guberti/CockcroftWalton/photos/IMG_20190924_183516.jpg

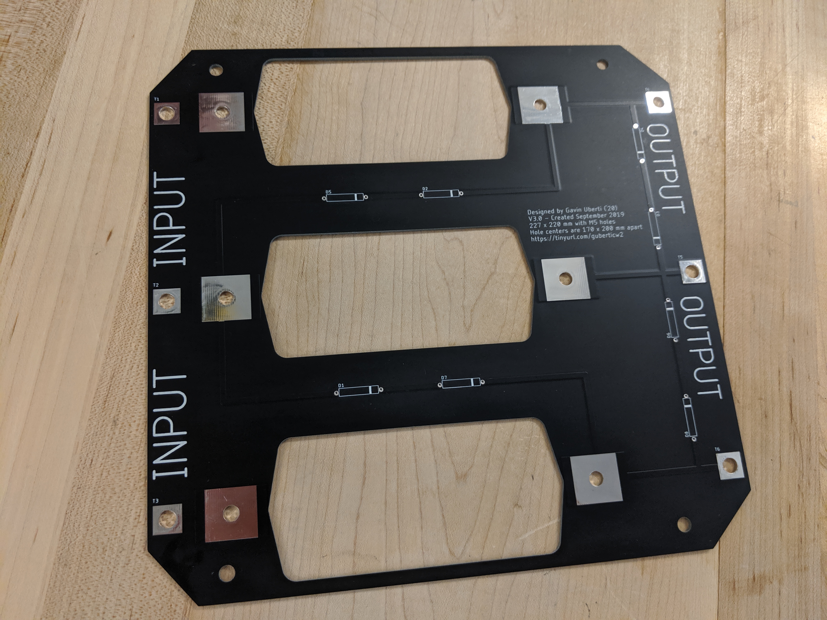
photos/IMG_20190924_183516.jpg
