guberti/CockcroftWalton/photos/IMG_20190929_215728.jpg

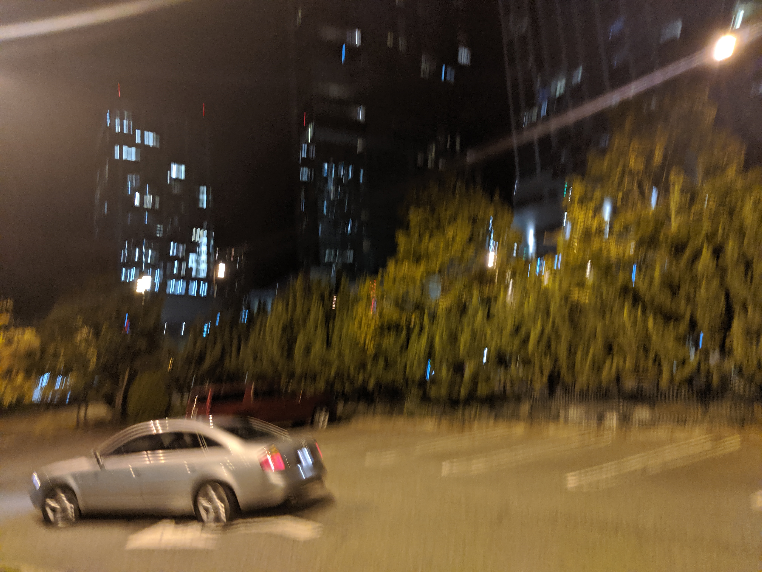
photos/IMG_20190929_215728.jpg
