guberti/CockcroftWalton/photos/IMG_20191001_172126_1.jpg

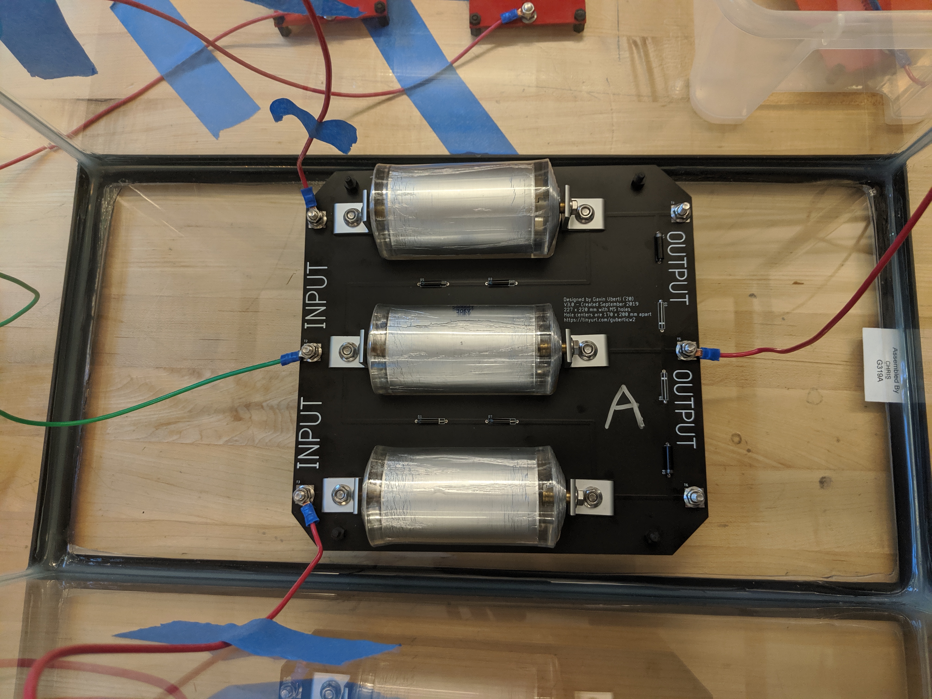
photos/IMG_20191001_172126_1.jpg
