guberti/CockcroftWalton/photos/IMG_20191002_173049.jpg

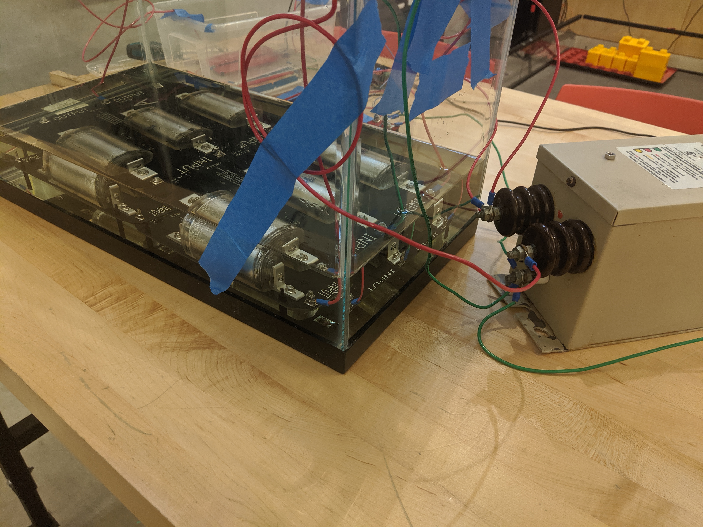
photos/IMG_20191002_173049.jpg
