guberti/CockcroftWalton/photos/IMG_20191002_173056.jpg

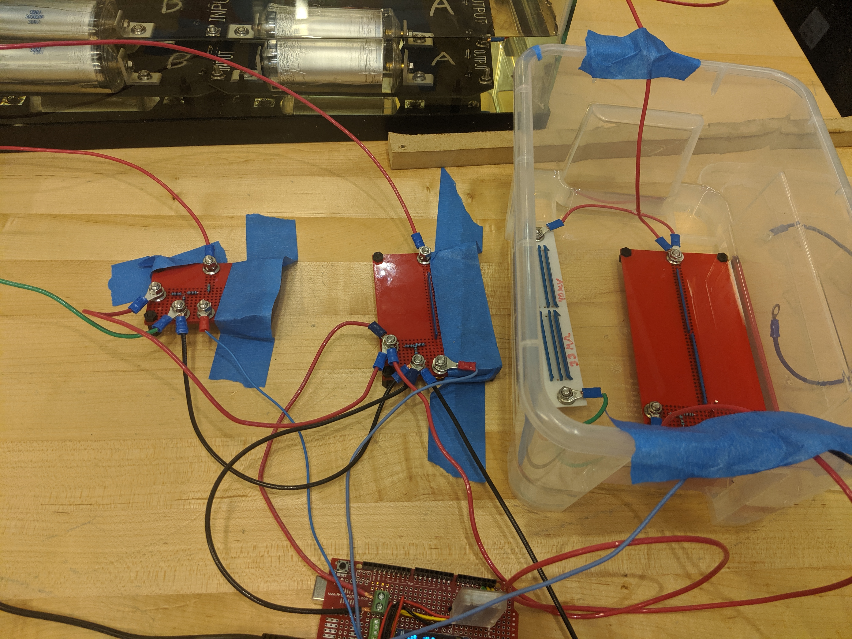
photos/IMG_20191002_173056.jpg
