guberti/CockcroftWalton/photos/IMG_20191002_173057.jpg

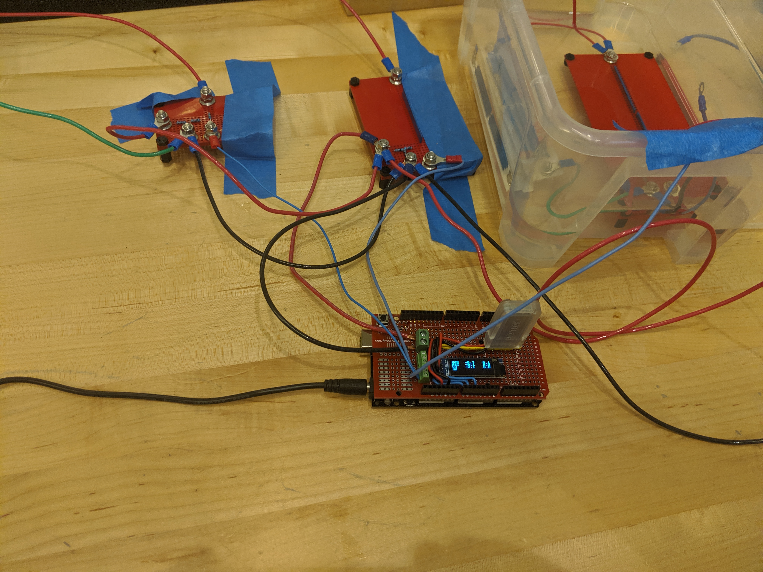
photos/IMG_20191002_173057.jpg
