guberti/CockcroftWalton/photos/IMG_20191002_173058.jpg

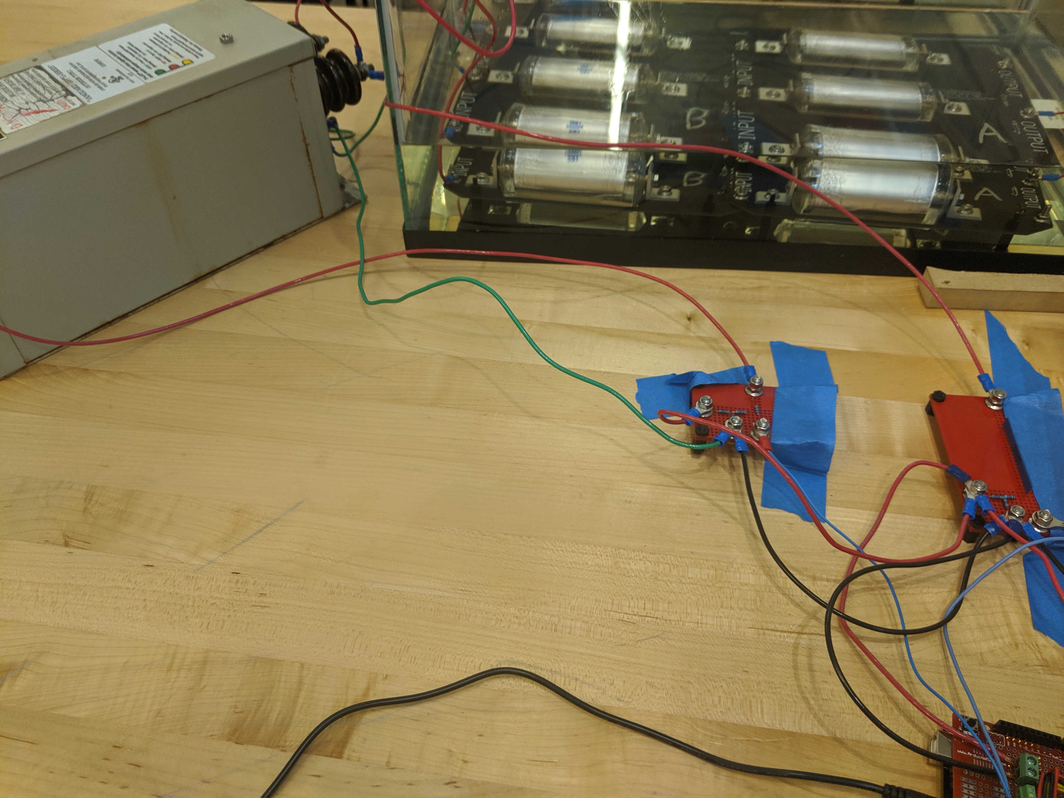
photos/IMG_20191002_173058.jpg
