guberti/CockcroftWalton/photos/IMG_20191002_173100.jpg

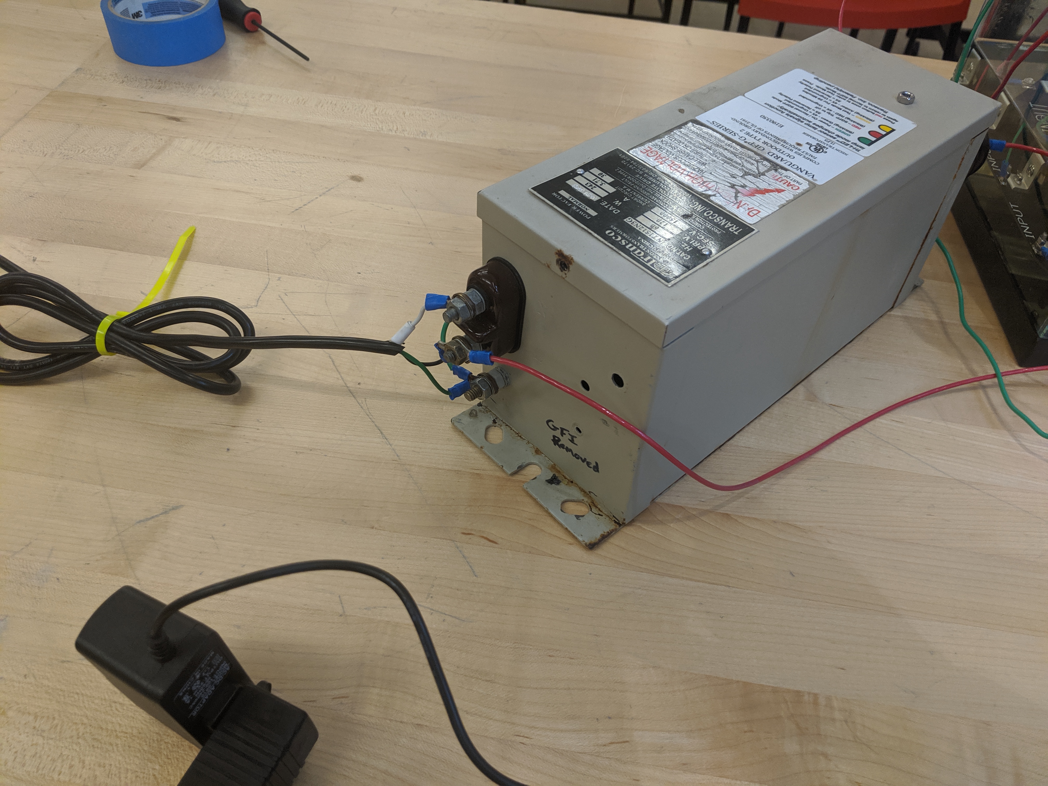
photos/IMG_20191002_173100.jpg
