guberti/CockcroftWalton/photos/IMG_20191002_173102.jpg

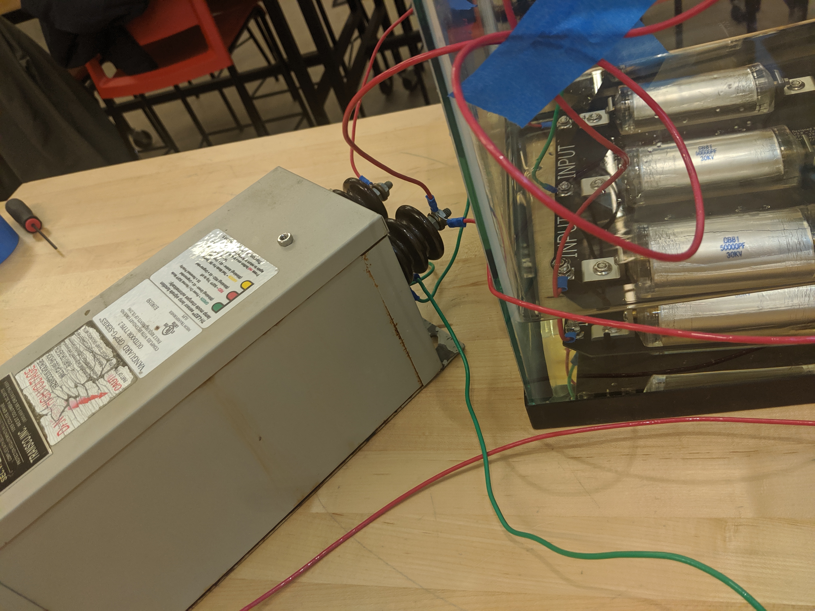
photos/IMG_20191002_173102.jpg
