guberti/CockcroftWalton/photos/IMG_20191002_173109.jpg

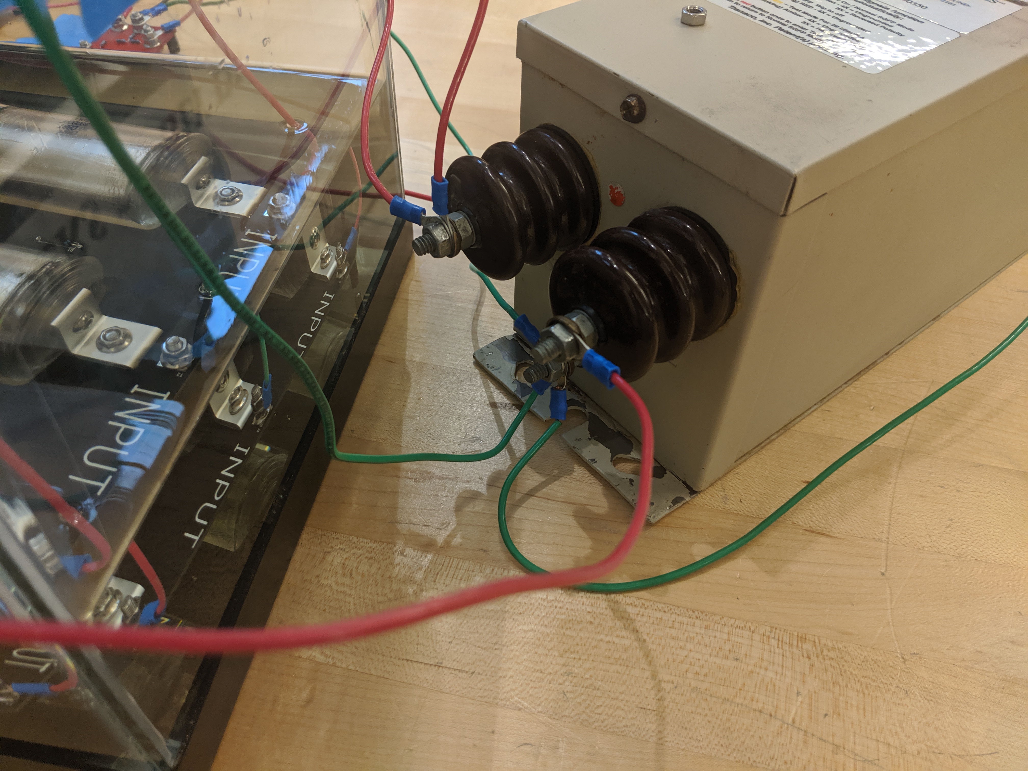
photos/IMG_20191002_173109.jpg
